heyspacebuck/SMOL/img/assm/half-melted paste.jpg

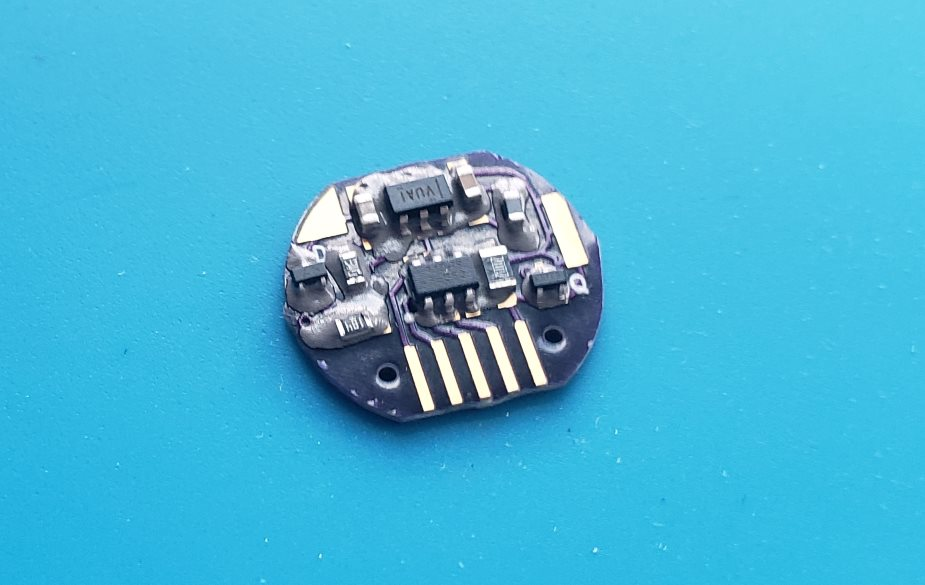
img/assm/half-melted paste.jpg
