heyspacebuck/SMOL/img/breadboard.jpg

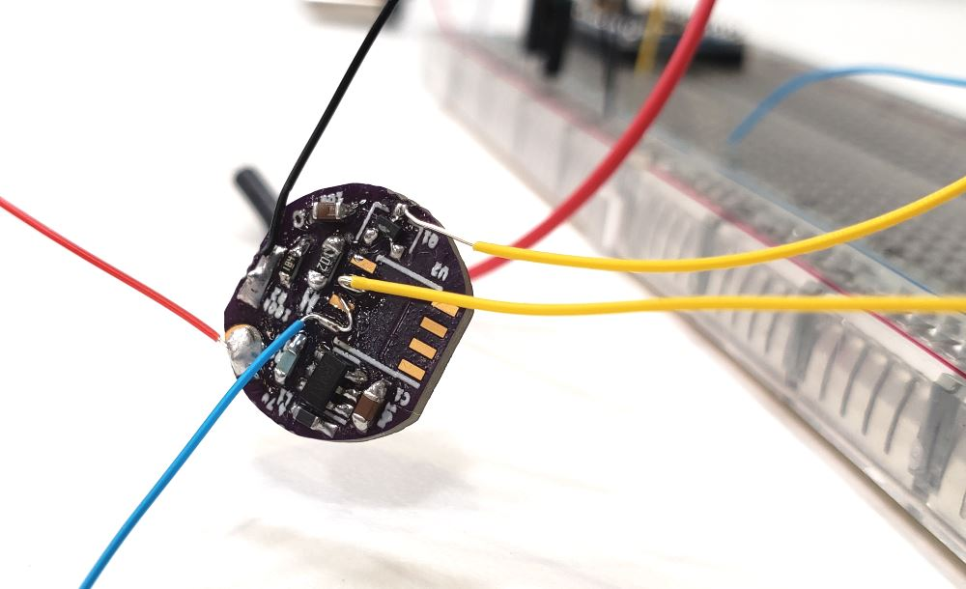
img/breadboard.jpg
