heyspacebuck/SMOL/img/pogopins.jpg

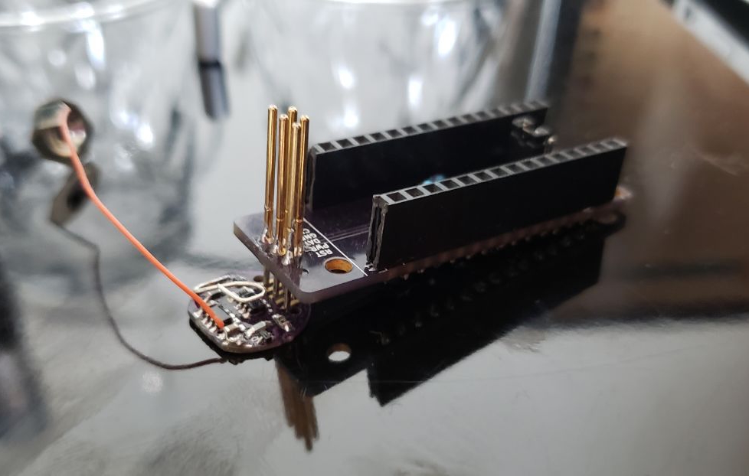
img/pogopins.jpg
