heyspacebuck/SMOL/img/revs/r6_p2_b.png

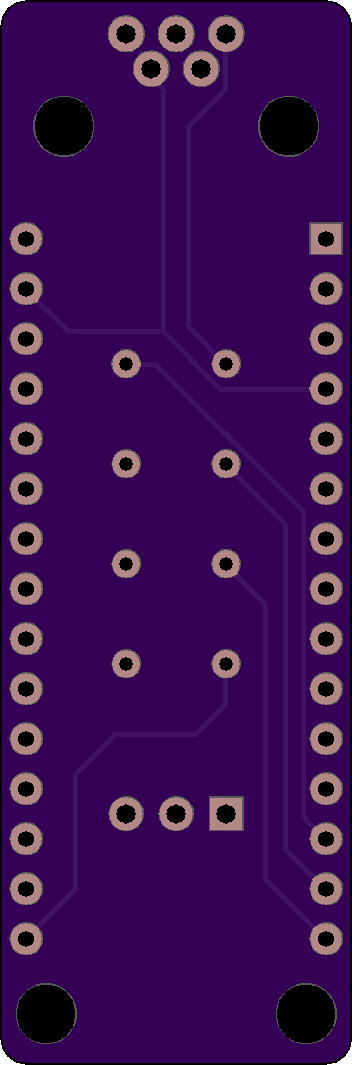
img/revs/r6_p2_b.png
