heyspacebuck/SMOL/img/revs/r6_p2_t.png

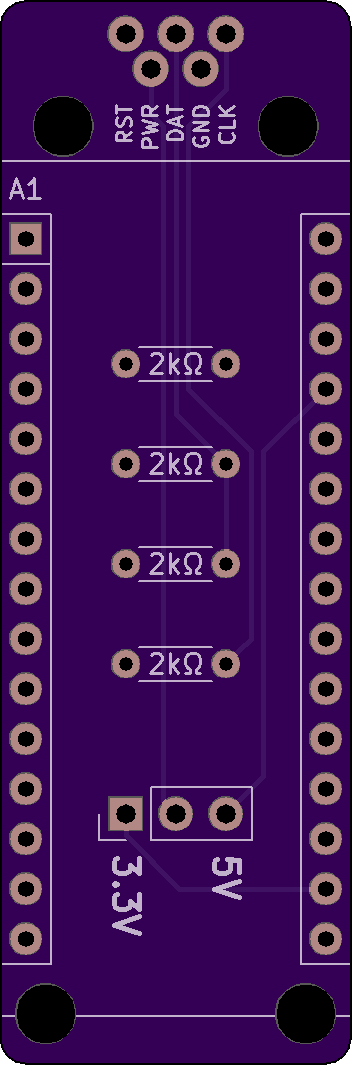
img/revs/r6_p2_t.png
