heyspacebuck/SMOL/Code examples/4. Morse Code ILOVEYOU/MorseAlphabet.h

#ifndef MORSEALPHABET_H
#define MORSEALPHABET_H
  void OCR0A_idle();
  void Dot();
  void Dash();
  void Pause();
  void A();
  void B();
  void C();
  void D();
  void E();
  void F();
  void G();
  void H();
  void I();
  void J();
  void K();
  void L();
  void M();
  void N();
  void O();
  void P();
  void Q();
  void R();
  void S();
  void T();
  void U();
  void V();
  void W();
  void X();
  void Y();
  void Z();
  void Space();
#endif
